MALIKM987/Wzmacniacz_3W/materiały/PCB_Project.pdf

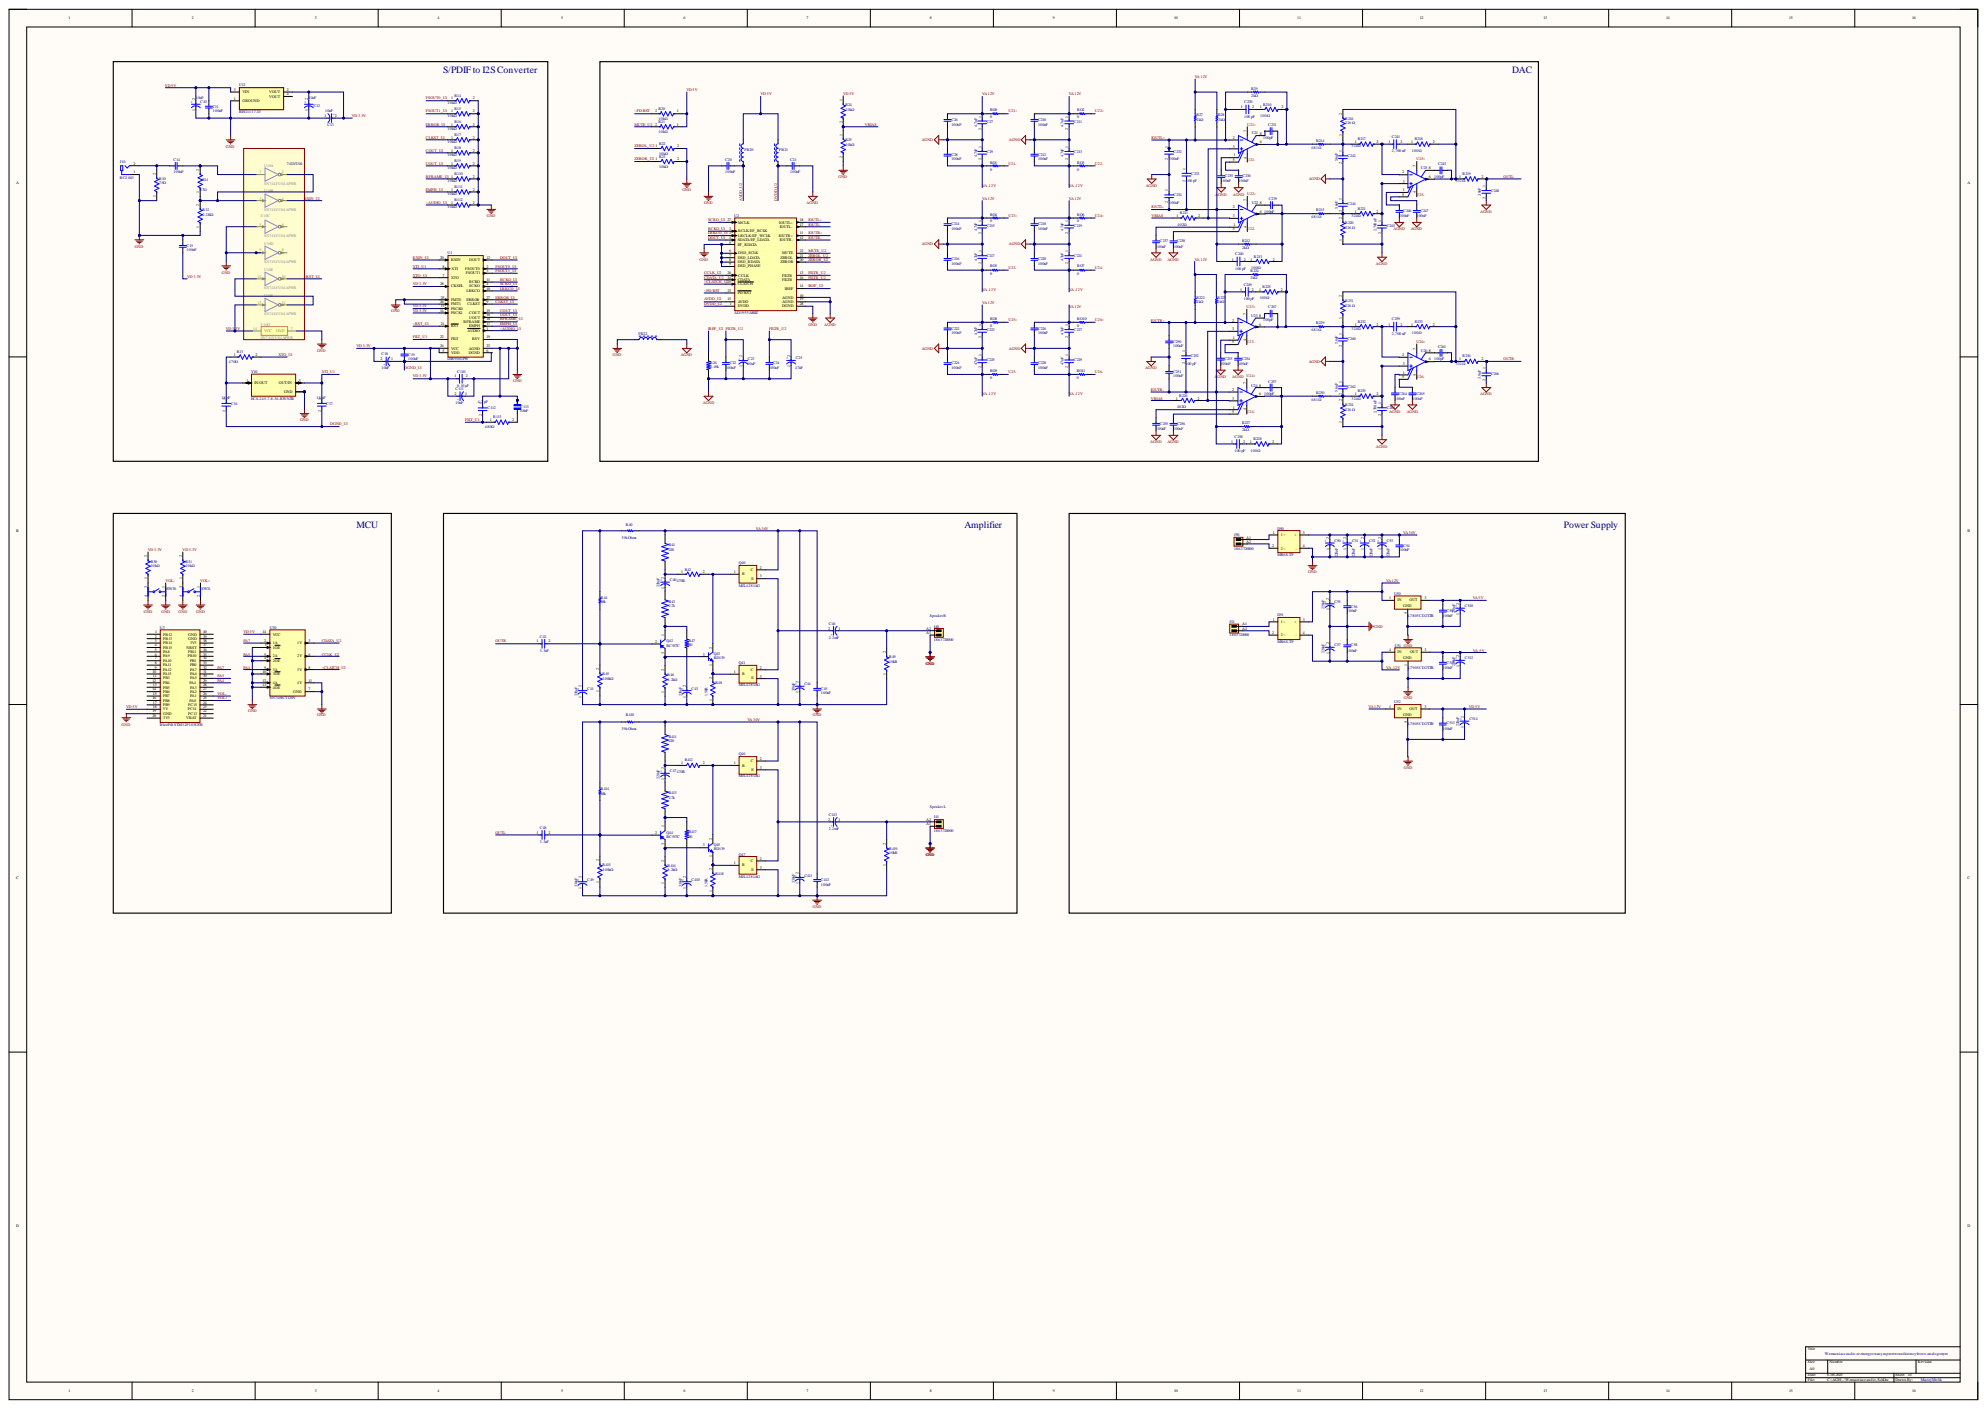
[picture p31: page 1]

U5 0 IN GND

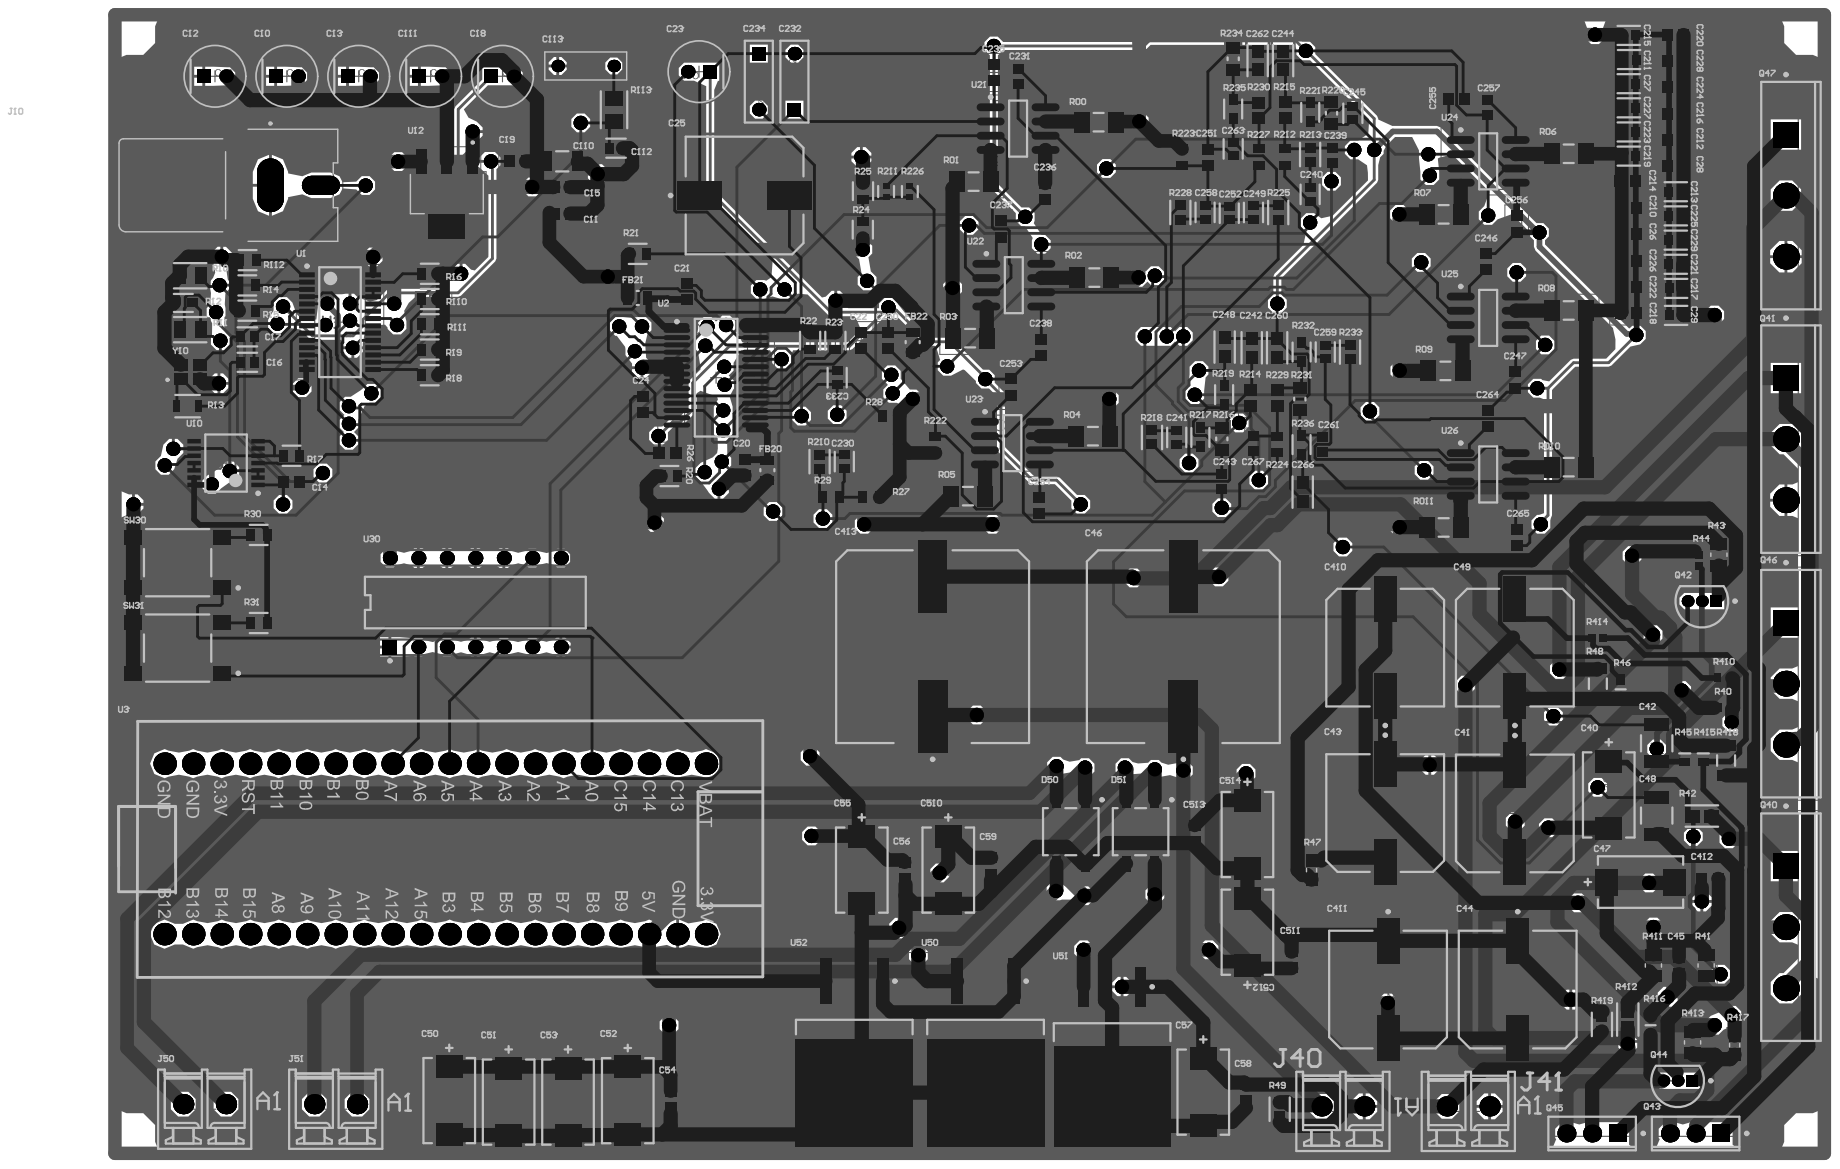
[picture p32: page 2]

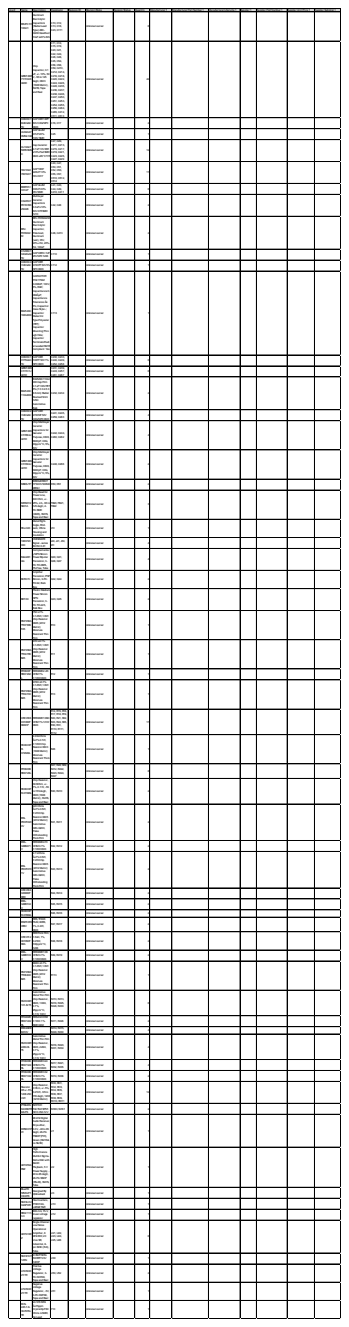
[picture p33: page 3]

GRM188R 71H104K A93D | Chip Capacitor, 0.1 uF, +/- 10%, 50 V, -55to125 degC, 0603 (1608Metric), RoHS, Tape andReel | C11, C14, C15, C19, C20, C21, C22, C24, C26, C28, C45, C54, C56, C58, C59, C210, C212, C214, C216, C218, C220, C222, C224, C226, C228, C235, C236, C237, C238, C246, C247, C250, C251, C253, C254, C255, C256, C264, C265, C412, C511, C513 | Unknownserver | 42

C0603C1 80J5GAC TU | CAPCER18PF 50VC0G/NP0 0603 | C16, C17 | Unknownserver | 2

UUX2A47 0MNL1GS | CAPALUM 47UF20% 100VSMD | C25 | Unknownserver | 1

CL10A47 5KP8NNN C | CapCeramic 4.7uF10VX5R ±10%PadSMD 0603+85°CT/R | C27, C29, C211, C213, C215, C217, C219, C221, C223, C225, C227, C229 | Unknownserver | 12

T491D22 7K016AT | CAPTANT 220UF10% 16V2917 | C40, C47, C50, C51, C52, C53, C55, C57, C510, C512, C514 | Unknownserver | 11

EEEFK1V 331AP | CAPALUM 330UF20% 35VSMD | C41, C43, C44, C49, C410, C411 | Unknownserver | 6

C3225X7 R1H335K 250AB | Multilayer Ceramic Capacitors 3.3uF±10% 50VX7RSMD 1210 | C42, C48 | Unknownserver | 2

EEV-FK1E222 M | EEV-FK1E222M Aluminum Electrolytic Capacitor, Polarized, Aluminum (wet), 35V, 20%+Tol, 20%-Tol, 100uF | C46, C413 | Unknownserver | 2

C1206C1 04G3GAC TU | CAPCER0.1UF 25VNP01206 | C110 | Unknownserver | 1

C0603C4 72J5GAC TU | CAPCER 4700PF50V5% NP00603 | C112 | Unknownserver | 1

B32529C 1683J000 | CAPACITOR POLYFILM 0.068UF, 100V, 5%, RAD; Capacitance:0. 068ÂµF; Capacitance Tolerance:Â± 5%; Capacitor CaseStyle:-; Capacitor Dielectric Type:Polyester (PET); Capacitor Mounting:Thro ughHole; Capacitor Terminals:Radi al LeadedRoHS Compliant: Yes | C113 | Unknownserver | 1

C0603C1 01F5GAC TU | CAPCER 100PF50V1% NP00603 | C230, C233, C240, C249, C252, C258 | Unknownserver | 6

GRM1885 C1H101J A01D | | C231, C239, C243, C257, C261, C267 | Unknownserver | 6

B32529C 1104J000 | B32529C1104J 000CapFilm 0.1uF100VPET 5%(7.3X2.5X 6.5mm) Radial Stacked5mm 125C Automotive Bulk | C232, C234 | Unknownserver | 2

C0603C2 72J5GAC TU | CAPCER 2700NF50V C0G/NP00603 | C241, C245, C259, C263 | Unknownserver | 4

GRM1885 C1H562J A01D | Chip Multilayer Ceramic Capacitors for General Purpose, 0603, 5600pF, C0G, 30ppm/°C, 5%, 50V | C242, C244, C260, C262 | Unknownserver | 4

GRM1885 C1H392J A01D | Chip Multilayer Ceramic Capacitors for General Purpose, 0603, 3900pF, C0G, 30ppm/°C, 5%, 50V | C248, C266 | Unknownserver | 2

MB6S-TP | BRIDGERECT 1P600V500MA MBS-1 | D50, D51 | Unknownserver | 2

MPZ2012 S601A | ChipBeadfor Power Line, 600Ohm, +/-25%, 2A, -55to 125degC, 2-PinSMD (0805), RoHS, TapeandReel | FB20, FB21, FB22 | Unknownserver | 3

RCJ-043 | Metal Right-Angle, RCA Jack, White Housingand Insulation | J10 | Unknownserver | 1

1863720 000 | OMNIMATE Signal - series BC/SC3.81 | J40, J41, J50, J51 | Unknownserver | 4

MJL4281 AG | Complementar yNPNSilicon Power Bipolar Transistor, 3-Pin TO-3BPL, Pb-Free, Tube | Q40, Q41, Q46, Q47 | Unknownserver | 4

BC557C | Amplifier Transistor, PNP Silicon, 3-Pin TO-92, Bulk Box | Q42, Q44 | Unknownserver | 2

BD139 | Plastic Medium-Power Silicon NPN Transistor, 3-Pin TO-225, BulkBox | Q43, Q45 | Unknownserver | 2

RN73R2A TTD75R0 F25 | 75Ω±1% 0.125W, 1/8W Chip Resistor 0805(2012 Metric) Moisture Resistant Thin Film | R10 | Unknownserver | 1

RN73R2A TTD47R0 B25 | 47Ω±0.1% 0.125W, 1/8W Chip Resistor 0805(2012 Metric) Moisture Resistant Thin Film | R11 | Unknownserver | 1

RT0603F RE072K2 L | RESSMD2.2K OHM1% 1/10W0603 | R12 | Unknownserver | 1

RN73R2A TTD4700 B25 | 470Ω±0.1% 0.125W, 1/8W Chip Resistor 0805(2012 Metric) Moisture Resistant Thin Film | R13 | Unknownserver | 1

CRCW06 0310K0F KEAHP | RESSMD10KΩ OHM1%1/3W 0603 | R14, R15, R16, R17, R18, R19, R20, R21, R22, R23, R24, R25, R30, R31, R110, R111, R112 | Unknownserver | 17

RC0603F R-072K49L | 2.49kOhms Â±1%0.1W, 1/10WChip Resistor 0603 (1608Metric) Moisture Resistant Thick Film | R26 | Unknownserver | 1

RT0603B RD072KL | | R27, R28, R29, R212, R222, R223, R224, R227 | Unknownserver | 8

RC0603F R-0739KL | Chip Resistor, 39KOhm, +/-1%, 0.1W, -55 to155degC, 0603(1608 Metric), RoHS, TapeandReel | R40, R410 | Unknownserver | 2

ERJ-P6WF220 0V | 220Ohms Â±1%0.5W, 1/2WChip Resistor 0805 (2012Metric) Automotive AEC-Q200, Pulse Withstanding Thick Film | R41, R411 | Unknownserver | 2

ERA-3AEB471 V | RESSMD470 OHM0.1% 1/10W0603 | R42, R412 | Unknownserver | 2

ERJ-P6WF270 1V | 2.7 kOhms Â±1%0.5W, 1/2WChip Resistor 0805 (2012Metric) Automotive AEC-Q200, Pulse Withstanding Thick Film | R43, R413 | Unknownserver | 2

CRCW04 0268K0F KED | | R44, R414 | Unknownserver | 2

ERA-3AEB104 V | | R45, R415 | Unknownserver | 2

RC0603F R-078K2L | | R46, R416 | Unknownserver | 2

ERJP03F8 0R6V | RES, THICK FILM, 80R6, 1%, 0.2W, 0603 | R47, R417 | Unknownserver | 2

CRCW12 061K50F KEA | RESThick Film, 1.5kΩ, 1%, 0.25W, 100ppm/°C, 1206 | R48, R418 | Unknownserver | 2

ERA-3AEB103 V | RESSMD10K OHM0.1% 1/10W0603 | R49, R419 | Unknownserver | 2

RN73R2A TTD6800 B25 | 680Ω±0.1% 0.125W, 1/8W Chip Resistor 0805(2012 Metric) Moisture Resistant Thin Film | R113 | Unknownserver | 1

RG1608P-101-B-T5 | Automotive Metal Thin Film Chip Resistor, 0603, 100Ω, 0.1%, 25ppm/°C, 0.1W, 100V | R210, R213, R218, R225, R228, R233 | Unknownserver | 6

RT0402B RD07402 RL | RES402OHM 1/16W.1% SMD0402 | R211, R226 | Unknownserver | 2

ERA3AEB 6810V | | R214, R215, R229, R230 | Unknownserver | 4

RG1608P-2260-B-T5 | Automotive Metal Thin Film Chip Resistor, 0603, 226Ω, 0.1%, 25ppm/°C, 0.1W, 100V | R216, R220, R231, R234 | Unknownserver | 4

RT0603B RD07324 RL | RESSMD324 OHM0.1% 1/10W0603 | R217, R221, R232, R235 | Unknownserver | 4

RT0603B RD07332 RL | RESSMD332 OHM0.1% 1/10W0603 | R219, R236 | Unknownserver | 2

Resistor 0R+/- 5% 1206250 mW | Chip Resistor, 0Ohm, +/- 5%, 0.25W, -55to 155degC, 1206 (3216Metric) | RO0, RO1, RO2, RO3, RO4, RO5, RO6, RO7, RO8, RO9, RO10, RO11 | Unknownserver | 12

PTS645S M43SMTR 92LFS | SWITCH TACTILESPST-NO0.05A12V | SW30, SW31 | Unknownserver | 2

DIR9001P W | 96kHzDigital Audio Receiver, 50ps Jitter, 3.3V, -40to85 degC, 28-Pin TSSOP(PW), Green(RoHS& noSb/Br) | U1 | Unknownserver | 1

AD1955A RSZ | High Performance Multibit Sigma-DeltaDACwith SACD Playback, 5V Power Supply, -40to85degC, 28-PinSSOP (RS-28), RoHS, Tube | U2 | Unknownserver | 1

BluePill STM32F1 03C8T6 | DesignedBy @Alixahedi | U3 | Unknownserver | 1

SN74LVU 04APWR | HexInverters, PW0014A, LARGET&R | U10 | Unknownserver | 1

REG1117-3.3 | 800-mA, 15-V, linear voltage regulator | U12 | Unknownserver | 1

AD797AR Z | SingleChannel LowNoise Operational Amplifier, 8 MHzBW, 20 V/usSR, Industrial, 8-pinSOIC(R-8), Tube | U21, U22, U23, U24, U25, U26 | Unknownserver | 6

SN74HCT 125N | ICBUFNON-INVERT5.5V 14DIP | U30 | Unknownserver | 1

L7805CD 2T-TR | Positive Voltage Regulator, 3-Pin D2PAK, TapeandReel | U50, U52 | Unknownserver | 2

L7905CD 2T-TR | Negative Voltage Regulator, -5V, 3-Pin D2PAK, TapeandReel | U51 | Unknownserver | 1

ECS-245.7-8-36-RWN-TR | 24.576MHz Â±15ppm Crystal 8pF60 Ohms4-SMD, NoLead | Y10 | Unknownserver | 1
