MALIKM987/Wzmacniacz_3W/sym/amplifier.asc

B1: bv; V =0.2*(sin(2*pi*100*time) + 0.5*sin(2*pi*1k*time) + 0.2*sin(2*pi*5k*time) + 0.1*sin(2*pi*10k*time) + 0.05*sin(2*pi*20k*time))
C1: cap; 3.3µ; V=25
C2: cap; 330µ; V=25
C3: cap; 330µ; V=25
C4: cap; 220µ; V=25
C5: cap; 2200µ; V=35
C6: cap; 330µ; V=25
C7: cap; 100n; V=50
C8: cap; 400µ
L1: ind; 800µ
L2: ind; 10m
Q4: pnp; BC557C
Q6: npn; MJL4281C
Q7: npn; Qbd139
Q8: npn; MJL4281C
R1: res; 68k; tol=1 pwr=0.25
R2: res; 100K; tol=1 pwr=0.25
R3: res; 8.2K; tol=1 pwr=0.25
R4: res; 80; tol=1 pwr=0.5
R5: res; 2.7K; tol=1 pwr=0.5
R6: res; 220; tol=1 pwr=0.5
R7: res; 39K; tol=1 pwr=0.25
R8: res; 470; tol=1 pwr=0.5
R9: res; 1.5k; tol=1 pwr=0.25
R10: res; 10K; tol=1 pwr=0.25
R11: res; 8
R12: res; 25
V1: voltage; 36
V2: voltage; SINE(0 0.5 1k); AC 0.5
Named nets: 0, +VCC, INPUT, OUTPUT
.tran 10m
.meas P_rms RMS V(n007)*I(R11)
.ac dec 100 1 300000k
.MODEL Qbd139 npn
+IS=1e-09 BF=222.664 NF=0.85 VAF=36.4079
+IKF=0.166126 ISE=5.03418e-09 NE=1.45313 BR=1.35467
+NR=1.33751 VAR=142.931 IKR=1.66126 ISC=5.02557e-09
+NC=3.10227 RB=26.9143 IRB=0.1 RBM=0.1
+RE=0.000472454 RC=1.04109 XTB=0.727762 XTI=1.04311
+EG=1.05 CJE=1e-11 VJE=0.75 MJE=0.33
+TF=1e-09 XTF=1 VTF=10 ITF=0.01
+CJC=1e-11 VJC=0.75 MJC=0.33 XCJC=0.9
+FC=0.5 CJS=0 VJS=0.75 MJS=0.5
+TR=1e-07 PTF=0 KF=0 AF=1
* Model generated on Feb 14, 2004
* Model format: PSpice
.MODEL MJL4281C npn
+IS=5e-12 BF=158 VAF=1000 IKF=50 ISE=20e-12 NE=1.5 NF=1.0
+RB=3.0 RC=0.1
+CJE=11e-9 MJE=0.35 VJE=0.5 RE=0.0
+CJC=1.2e-9 MJC=0.5 VJC=0.6 FC=0.1
+TF=2.7e-9 XTF=7500 VTF=3 ITF=750
+TR=100e-9 BR=5 VAR=4.3 NR=1.1
+EG=1.1 XCJC=1.0 XTB=0.12 XTI=1.0
+NC=4 ISC=0.3e-12
+IKR=4.4 CJS=0 VJS=0.75 MJS=0.5
+PTF=0 KF=0 AF=1 Vceo=200
+Icrating=15 mfg=CA041611
