MALIKM987/Wzmacniacz_3W/sym/Power supply.asc

C1: cap; 100n
C2: cap; 220µ
C3: cap; 100n
C4: cap; 100n
C5: cap; 220µ
C6: cap; 220µ
C7: cap; 220µ
C8: cap; 220µ
C9: cap; 220µ
D1: diode
D2: diode
D3: diode
D4: diode
D5: diode
D6: diode
D7: diode
D8: diode
L1: ind; 100µ
L2: ind; 5000µ
L3: ind; 1700µ
R1: res; 10k
R2: res; 10k
R3: res; 1
R4: res; 10k
R6: res; 1k
R7: res; 1k
V1: voltage; SINE(0 230 50)
Named nets: 0, 230V_AC, 12+, 12-, 38+
K1 L1 L2 L3 1
.tran 100
